travishermant/vikingbot2-ECE478/Documentation/Pictures/FrontView.jpeg

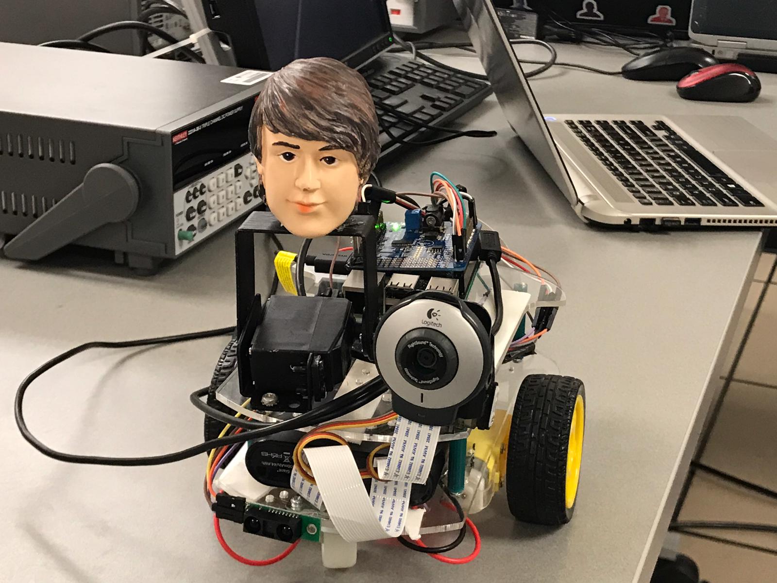
Documentation/Pictures/FrontView.jpeg
