travishermant/vikingbot2-ECE478/Documentation/Pictures/TopDown.png

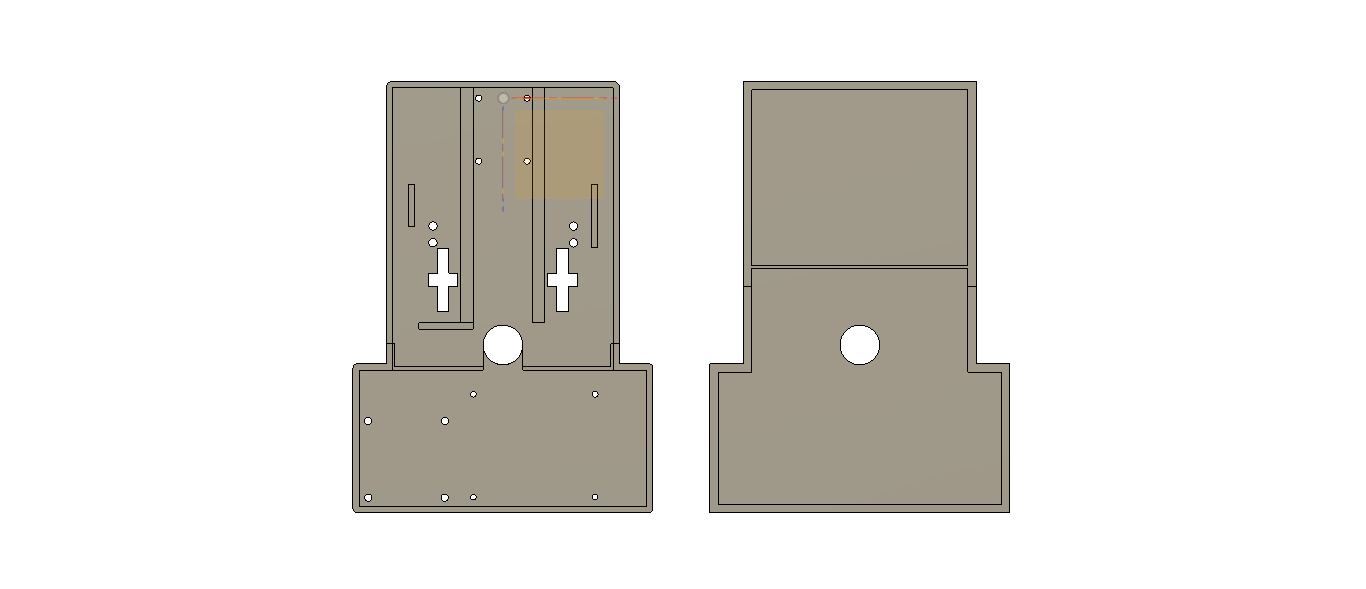
Documentation/Pictures/TopDown.png
